blaizard/alarm/model/0001.png

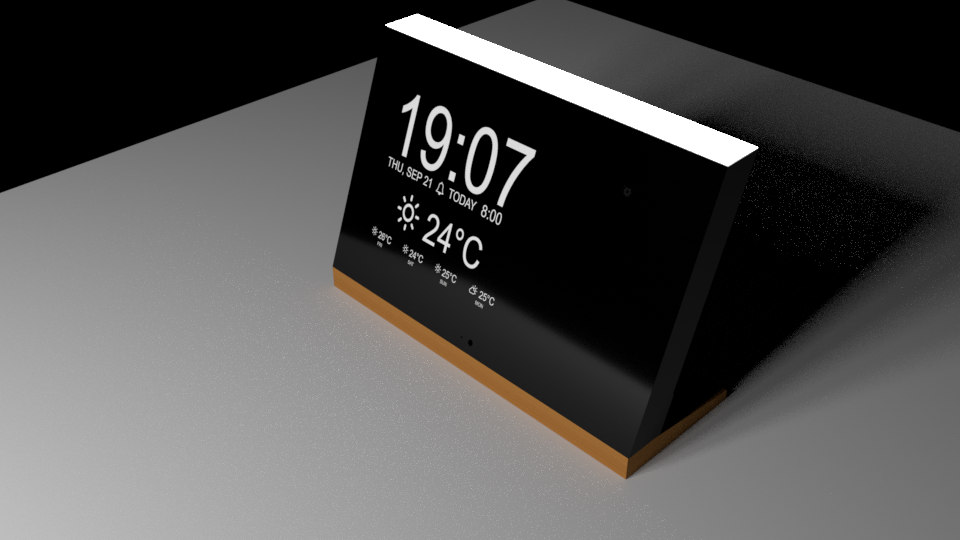
model/0001.png
