blaizard/alarm/model/default screen.jpg

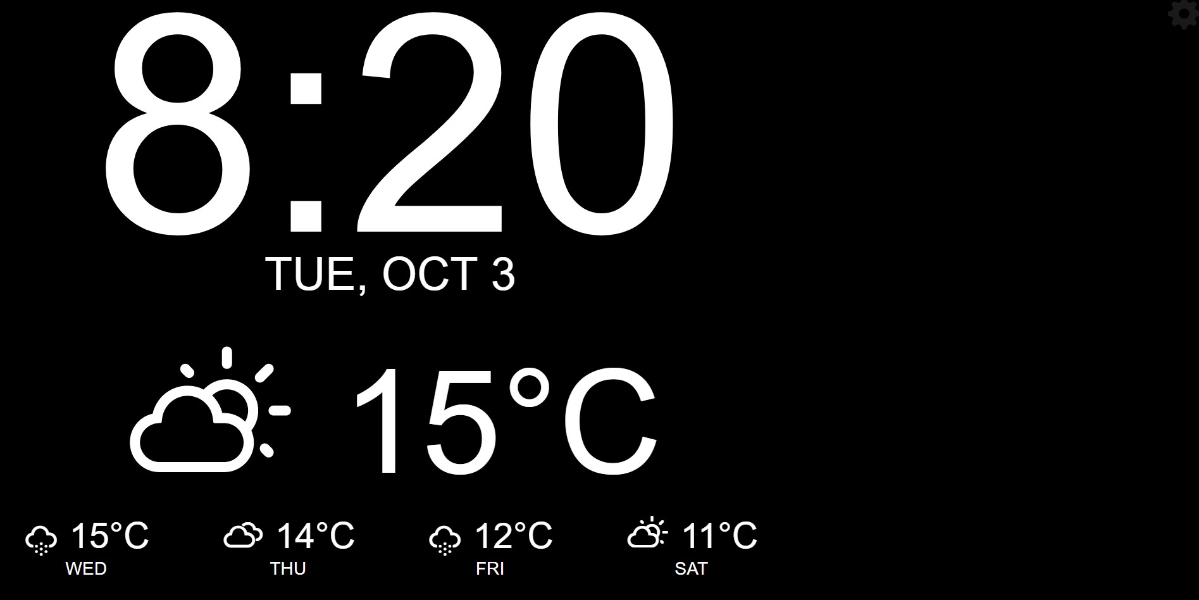
model/default screen.jpg
