blaizard/alarm/model/speaker.jpg

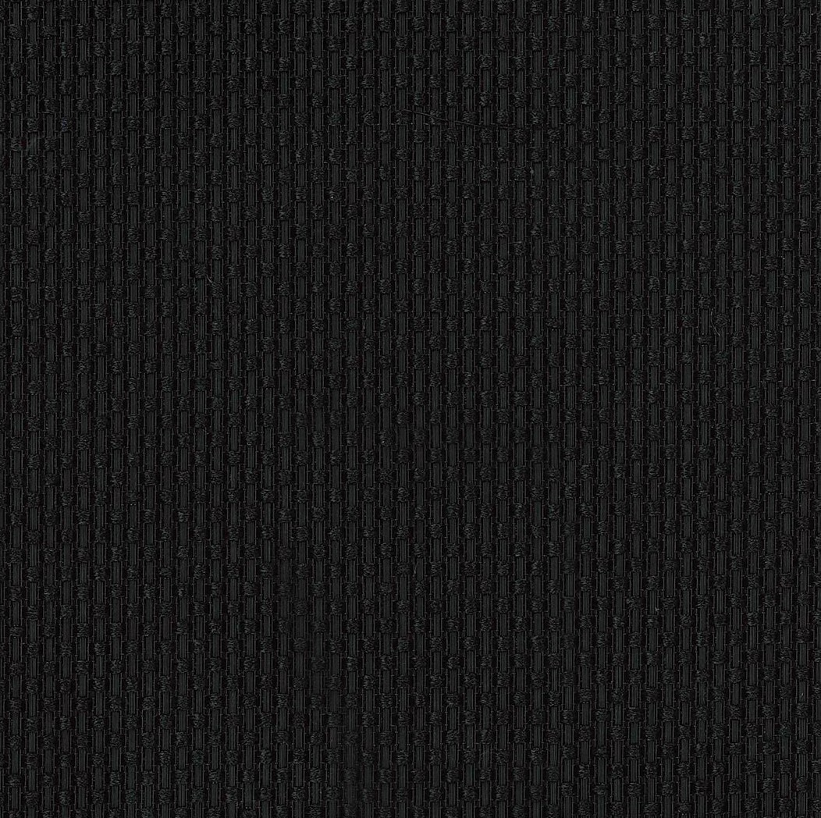
model/speaker.jpg
