blaizard/alarm/fw/samd21/GccQTouchApplication4/GccQTouchApplication4/touch.c

/* This source file is part of the ATMEL QTouch Library 5.0.7 */

/*****************************************************************************
 *
 * \file
 *
 * \brief  This file contains the SAMD QTouch library initialization,
 * sensor configuration and measurement routines.
 *
 *
 * - Userguide:          QTouch Library Peripheral Touch Controller User Guide.
 * - Support email:      www.atmel.com/design-support/
 *
 *
 * Copyright (c) 2013-2015 Atmel Corporation. All rights reserved.
 *
 * \asf_license_start
 *
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
 * 3. The name of Atmel may not be used to endorse or promote products derived
 *    from this software without specific prior written permission.
 *
 * 4. This software may only be redistributed and used in connection with an
 *    Atmel microcontroller product.
 *
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
 * \asf_license_stop
 *
 ******************************************************************************/

/*----------------------------------------------------------------------------
 *                               include files
 *
 *
 *----------------------------------------------------------------------------*/

/**
 * Includes for Touch Library.
 */

#include "touch_api_ptc.h"
#if (!defined(__D1x_NONASF__))
#include <asf.h>
#else
#define  NULL 0
#endif
/*----------------------------------------------------------------------------
 *                           manifest constants
 *
 *
 *----------------------------------------------------------------------------*/
#define   DEF_SELFCAP_CAL_SEQ1_COUNT                8
#define   DEF_SELFCAP_CAL_SEQ2_COUNT                4
#define DEF_SELFCAP_CC_CAL_CLK_PRESCALE_PER_NODE PRSC_DIV_SEL_1,PRSC_DIV_SEL_1,PRSC_DIV_SEL_1,PRSC_DIV_SEL_1
#define DEF_SELFCAP_CC_CAL_SENSE_RESISTOR_PER_NODE RSEL_VAL_0,RSEL_VAL_0,RSEL_VAL_0,RSEL_VAL_0
#define   DEF_SELFCAP_QUICK_REBURST_ENABLE          1u

/*----------------------------------------------------------------------------
 *                                   macros
 *
 *
 *----------------------------------------------------------------------------*/

/*----------------------------------------------------------------------------
 *                           type definitions
 *
 *
 *----------------------------------------------------------------------------*/

/*----------------------------------------------------------------------------
 *                           Structure Declarations
 *
 *
 *----------------------------------------------------------------------------*/

/*----------------------------------------------------------------------------
 *                               global variables
 *
 *
 *----------------------------------------------------------------------------*/
/* ! QTouch Library Timing info. */
touch_time_t touch_time;

/* ! QTouch Library acquisition status */
touch_acq_status_t  touch_acq_status;
/**
 * Mutual Cap sensors measured data pointer.
 * Note: This pointer is initialized by the QTouch library once the
 * touch_mutlcap_sensors_init API is called. */
touch_measure_data_t *p_mutlcap_measure_data = NULL;

/**
 * Self Cap sensors measured data pointer.
 * Note: This pointer is initialized by the QTouch library once the
 * touch_selfcap_sensors_init API is called. */
touch_measure_data_t *p_selfcap_measure_data = NULL;

/*----------------------------------------------------------------------------
 *                               static variables
 *
 *
 *----------------------------------------------------------------------------*/

/**
 * Self Cap sensors data block provided as input to Touch library.
 */
static uint8_t selfcap_data_blk[PRIV_SELFCAP_DATA_BLK_SIZE];

/**
 * Self Cap sensors Pins Info.
 */

uint32_t selfcap_y_nodes[DEF_SELFCAP_NUM_CHANNELS] = {DEF_SELFCAP_LINES};

filter_level_t selfcap_filter_level_per_node[DEF_SELFCAP_NUM_CHANNELS] = {DEF_SELFCAP_FILTER_LEVEL_PER_NODE};
	
uint8_t selfcap_auto_os_per_node[DEF_SELFCAP_NUM_CHANNELS]= {DEF_SELFCAP_AUTO_OS_PER_NODE};

gain_t selfcap_gain_per_node[DEF_SELFCAP_NUM_CHANNELS] = {DEF_SELFCAP_GAIN_PER_NODE};

rsel_val_t selfcap_resistor_per_node[DEF_SELFCAP_NUM_CHANNELS] = {DEF_SELFCAP_SENSE_RESISTOR_PER_NODE};

prsc_div_sel_t selfcap_prsc_per_node[DEF_SELFCAP_NUM_CHANNELS] = {DEF_SELFCAP_CLK_PRESCALE_PER_NODE};

prsc_div_sel_t selfcap_boot_prsc_per_node[DEF_SELFCAP_NUM_CHANNELS] = {DEF_SELFCAP_CC_CAL_CLK_PRESCALE_PER_NODE};

rsel_val_t selfcap_boot_resistor_per_node[DEF_SELFCAP_NUM_CHANNELS] = { DEF_SELFCAP_CC_CAL_SENSE_RESISTOR_PER_NODE};
	
freq_hop_sel_t selfcap_freq_hops[3u] = {DEF_SELFCAP_HOP_FREQS};

/**
 * Self Cap Configuration structure provided as input to Touch Library.
 *
 * Note: Use the touch.h configuration header file to fill in
 * the elements of this structure.  DO NOT modify any of the input values
 * directly in this structure.
 */
static touch_selfcap_config_t selfcap_config = {
	DEF_SELFCAP_NUM_CHANNELS,           /* Self Cap number of channels. */
	DEF_SELFCAP_NUM_SENSORS,            /* Self Cap number of sensors. */
	DEF_SELFCAP_NUM_ROTORS_SLIDERS,     /* Self Cap number of rotors and
	                                     * sliders. */

	/* Self Cap GLOBAL SENSOR CONFIGURATION INFO. */
	{
		DEF_SELFCAP_DI,                 /* uint8_t  di; Sensor detect
		                                 * integration (DI) limit. */

		/* Interchanging Negative and Positive Drift rate, since Signal
		 * increases on Touch. */
		DEF_SELFCAP_ATCH_DRIFT_RATE,    /* uint8_t  neg_drift_rate;
		                                 * Sensor
		                                 * negative drift rate. */
		DEF_SELFCAP_TCH_DRIFT_RATE,     /* uint8_t  pos_drift_rate;
		                                 * Sensor
		                                 * positive drift rate. */
		DEF_SELFCAP_MAX_ON_DURATION,    /* uint8_t  max_on_duration;
		                                 * Sensor
		                                 * maximum on duration. */
		DEF_SELFCAP_DRIFT_HOLD_TIME,    /* uint8_t  drift_hold_time;
		                                 * Sensor
		                                 * drift hold time. */
		DEF_SELFCAP_ATCH_RECAL_DELAY,   /* uint8_t  pos_recal_delay;
		                                 * Sensor positive recalibration
		                                 * delay. */

		DEF_SELFCAP_CAL_SEQ1_COUNT,
		DEF_SELFCAP_CAL_SEQ2_COUNT,
		DEF_SELFCAP_ATCH_RECAL_THRESHOLD, /* recal_threshold_t
		                                   * recal_threshold; Sensor
		                                   * recalibration threshold. */
		DEF_SELFCAP_TOUCH_POSTPROCESS_MODE,
        DEF_SELFCAP_AUTO_OS_SIGNAL_STABILITY_LIMIT,
		DEF_SELFCAP_FREQ_AUTO_TUNE_SIGNAL_STABILITY_LIMIT,
		DEF_SELFCAP_FREQ_AUTO_TUNE_IN_CNT,
		DEF_SELFCAP_NOISE_MEAS_SIGNAL_STABILITY_LIMIT, /* signal
		                                                *stability */
		DEF_SELFCAP_NOISE_LIMIT,
		DEF_SELFCAP_LOCKOUT_SEL,
		DEF_SELFCAP_LOCKOUT_CNTDOWN,
		#if ((SAMC20) || (SAMC21) || (SAML22))
		DEF_SELF_CAP_CSD_VALUE,
		#endif
	},
	{
		selfcap_gain_per_node,      /* Self Cap channel gain setting. */
		DEF_SELFCAP_FREQ_MODE,      /* Self Cap noise counter measure
		                             * enable/disable. */
		selfcap_prsc_per_node,
		selfcap_resistor_per_node,
		selfcap_boot_prsc_per_node,
		selfcap_boot_resistor_per_node,
		selfcap_freq_hops,
		selfcap_filter_level_per_node,   /* Self Cap filter level setting. */
		selfcap_auto_os_per_node,        /* Self Cap auto oversamples
		                             *setting. */
	},
	selfcap_data_blk,                   /* Self Cap data block index. */
	PRIV_SELFCAP_DATA_BLK_SIZE,         /* Self Cap data block size. */
	selfcap_y_nodes,                    /* Self Cap channel nodes. */
	DEF_SELFCAP_QUICK_REBURST_ENABLE,
	DEF_SELFCAP_FILTER_CALLBACK,         /* Self Cap filter callback
	                                      * function
	                                      * pointer. */
	DEF_SELFCAP_FREQ_AUTO_TUNE_ENABLE,
	DEF_SELFCAP_NOISE_MEAS_ENABLE,
	DEF_SELFCAP_NOISE_MEAS_BUFFER_CNT,
	DEF_SELFCAP_MOIS_TOLERANCE_ENABLE,
  	DEF_SELFCAP_NUM_MOIS_GROUPS,
    DEF_SELFCAP_MOIS_QUICK_REBURST_ENABLE,
    DEF_SELFCAP_PTC_GPIO_STATE,
	  .tlib_feature_list ={
		  .lk_chk = DEF_LOCKOUT_FUNC,
		  .auto_os_init = DEF_AUTO_OS_FUNC,//auto_os_resolve,
		  .auto_tune_init = DEF_SELF_AUTO_TUNE_FUNC,// self_auto_tuning
		  .enable_aks = DEF_AKS_FUNC, /*AKS grouping function */
	  }
};

/**
 * Touch Library input configuration structure.
 */
touch_config_t touch_config = {
	NULL,
	&selfcap_config,                /* Pointer to Self Cap configuration
	                                 * structure. */
	DEF_TOUCH_PTC_ISR_LVL,          /* PTC interrupt level. */
};

/*----------------------------------------------------------------------------
 *                               prototypes
 *
 *
 *----------------------------------------------------------------------------*/

/*! \brief configure keys, rotors and sliders.
 */
static touch_ret_t touch_sensors_config(void);

/*! \brief Self Cap measure complete callback function example prototype.
 */
void touch_selfcap_measure_complete_callback( void );

/*! \brief Initialize and enable PTC clock.
 */
void touch_configure_ptc_clock(void);

void touch_std_err_handle(void);

void __attribute__((optimize("O0"))) touch_app_err_handler(touch_app_err_t touch_app_err_val, touch_ret_t touch_lib_err_val);

/*----------------------------------------------------------------------------
 *  static functions
 *
 *
 *----------------------------------------------------------------------------*/

void touch_configure_ptc_clock(void)
{
#if (!defined(__D1x_NONASF__))
	struct system_gclk_chan_config gclk_chan_conf;

	system_gclk_chan_get_config_defaults(&gclk_chan_conf);

	gclk_chan_conf.source_generator = GCLK_GENERATOR_1;

	system_gclk_chan_set_config(PTC_GCLK_ID, &gclk_chan_conf);

	system_gclk_chan_enable(PTC_GCLK_ID);

	#if (SAML21)
    system_apb_clock_set_mask(SYSTEM_CLOCK_APB_APBD, MCLK_APBDMASK_PTC);
    #elif ((SAMC20) || (SAMC21) || (SAML22))
	system_apb_clock_set_mask(SYSTEM_CLOCK_APB_APBC, MCLK_APBCMASK_PTC);
	#else
    system_apb_clock_set_mask(SYSTEM_CLOCK_APB_APBC, PM_APBCMASK_PTC);
    #endif
#else
	PM->APBCMASK.reg |= (1u << 11u);
#endif
}

void touch_std_err_handle(void)
{
	for(;;)
	{
		
	}
}

void  __attribute__((optimize("O0"))) touch_app_err_handler(touch_app_err_t touch_app_err_val, touch_ret_t touch_lib_err_val)
{
	if(DEF_TOUCH_APP_ERR_HANDLER)
	
	{
	switch(touch_app_err_val)
	{
		case TOUCH_INIT_CONFIG_ERR:
				/*Probable reason: the touch_xxxxcap_sensors_init is fed with an
				 incompatible / incomplete parameter*/
				touch_std_err_handle();
				break;
		case TOUCH_SENSOR_CONFIG_ERR:
				/*Probable reason: touch_xxxxcap_sensor_config is fed with an incompatible
				 parameter / Library state is not INIT*/
				touch_std_err_handle();
				break;
		case TOUCH_INIT_CALIB_ERR:
				/*Probable reason: the touch_xxxxcap_sensors_calibrate is fed with an
				invalid parameter / the LIB state is NONE/BUSY */
				touch_std_err_handle();
				break;
		case TOUCH_MEASURE_INCOMPLETE:
				/* Reaching this point can be due to - The touch_measure api has error 
				due to a invalid input param / it was on an invalid Touch Library state*/
				touch_std_err_handle();
				break;				
		case TOUCH_MEASURE_CC_CAL_FAILED:
				/*Probable reason: Hardware calibration error, check the hardware,
                  and ensure it is proper, if the error persists check the user manual
				  for sensor design guidelines*/
				touch_std_err_handle();
				break;	
		default:
				touch_std_err_handle();	
				break;
	}
	}
}

/* ! [setup] */

/*! \brief Example application entry function.
 */
touch_ret_t touch_sensors_init(void)
{
	touch_ret_t touch_ret = TOUCH_SUCCESS;

	/* Setup and enable generic clock source for PTC module. */
	touch_configure_ptc_clock();

	touch_time.measurement_period_ms = DEF_TOUCH_MEASUREMENT_PERIOD_MS;

	/* Initialize touch library for Self Cap operation. */
	touch_ret = touch_selfcap_sensors_init(&touch_config);
	if (touch_ret != TOUCH_SUCCESS) {
		touch_app_err_handler(TOUCH_INIT_CONFIG_ERR, touch_ret);
	}

#if DEF_TOUCH_QDEBUG_ENABLE == 1
	QDebug_Init();
#endif

	/* configure the touch library sensors. */
	touch_ret = touch_sensors_config();
	if (touch_ret != TOUCH_SUCCESS) {
		touch_app_err_handler(TOUCH_SENSOR_CONFIG_ERR, touch_ret);
	}

	/* Auto Tuning setting for calibration.
	 *
	 * AUTO_TUNE_PRSC: When Auto tuning of pre-scaler is selected
	 * the PTC uses the user defined internal series resistor setting
	 * (DEF_MUTLCAP_SENSE_RESISTOR) and the pre-scaler is adjusted
	 * to slow down the PTC operation to ensure full charge transfer.
	 *
	 * AUTO_TUNE_RSEL: When Auto tuning of the series resistor is
	 * selected the PTC runs at user defined pre-scaler setting speed
	 * (DEF_MUTLCAP_CLK_PRESCALE) and the internal series resistor is
	 * tuned automatically to the optimum value to allow for full
	 * charge transfer.
	 *
	 * AUTO_TUNE_NONE: When manual tuning option is selected
	 *(AUTO_TUNE_NONE),
	 * the user defined values of PTC pre-scaler and series resistor is used
	 * for PTC operation as given in DEF_MUTLCAP_CLK_PRESCALE and
	 * DEF_MUTLCAP_SENSE_RESISTOR
	 *
	 */
	touch_ret = touch_selfcap_sensors_calibrate(DEF_SELF_AUTO_TUNE_VALUE);
	if (touch_ret != TOUCH_SUCCESS) {
		touch_app_err_handler(TOUCH_INIT_CALIB_ERR, touch_ret);
	}

	return (touch_ret);
}

touch_ret_t touch_sensors_measure(void)
{
	touch_ret_t touch_ret = TOUCH_SUCCESS;
    if (!(p_selfcap_measure_data->acq_status & TOUCH_CC_CALIB_ERROR) || (!DEF_TOUCH_APP_ERR_HANDLER))
       {

	if (touch_time.time_to_measure_touch == 1u) {
		touch_ret = touch_selfcap_sensors_measure(
				touch_time.current_time_ms,
				NORMAL_ACQ_MODE,
				touch_selfcap_measure_complete_callback);

		if ((touch_ret != TOUCH_ACQ_INCOMPLETE) &&
				(touch_ret == TOUCH_SUCCESS)) {
			touch_time.time_to_measure_touch = 0u;
		} else if ((touch_ret != TOUCH_SUCCESS) &&
				(touch_ret != TOUCH_ACQ_INCOMPLETE)) {
					touch_app_err_handler(TOUCH_MEASURE_INCOMPLETE, touch_ret);
			/* Reaching this point can be due to -
			 *     1. The api has retured an error due to a invalid
			 * input parameter.
			 *     2. The api has been called during a invalid Touch
			 * Library state. */
			 }
		}
	}
    else
    {
		/*
        To find which sensor failed in the calibration, check
         p_xxxxcap_measure_data->p_sensors[<sensor>].state == SENSOR_CALIBRATION_ERROR
        */
		touch_app_err_handler(TOUCH_MEASURE_CC_CAL_FAILED, touch_ret);
    }

	return (touch_ret);
}

/*! \brief Example configuration for touch keys, rotors and sliders.
 *
 * \retval TOUCH_SUCCESS   Configuration setting successful.
 * \retval TOUCH_INVALID_xx   Invalid input configuration setting.
 */
touch_ret_t touch_sensors_config(void)
{
	touch_ret_t touch_ret = TOUCH_SUCCESS;
	sensor_id_t sensor_id;

		touch_ret = touch_selfcap_sensor_config(SENSOR_TYPE_KEY, CHANNEL_0,CHANNEL_0, NO_AKS_GROUP, 10u, HYST_25,RES_8_BIT, &sensor_id);
	if (touch_ret != TOUCH_SUCCESS)
	{
		 touch_app_err_handler(TOUCH_SENSOR_CONFIG_ERR, touch_ret); 
	}


	touch_ret = touch_selfcap_sensor_config(SENSOR_TYPE_KEY, CHANNEL_1,CHANNEL_1, NO_AKS_GROUP, 10u, HYST_25,RES_8_BIT, &sensor_id);
	if (touch_ret != TOUCH_SUCCESS)
	{
		 touch_app_err_handler(TOUCH_SENSOR_CONFIG_ERR, touch_ret); 
	}


	touch_ret = touch_selfcap_sensor_config(SENSOR_TYPE_KEY, CHANNEL_2,CHANNEL_2, NO_AKS_GROUP, 10u, HYST_25,RES_8_BIT, &sensor_id);
	if (touch_ret != TOUCH_SUCCESS)
	{
		 touch_app_err_handler(TOUCH_SENSOR_CONFIG_ERR, touch_ret); 
	}


	touch_ret = touch_selfcap_sensor_config(SENSOR_TYPE_KEY, CHANNEL_3,CHANNEL_3, NO_AKS_GROUP, 10u, HYST_25,RES_8_BIT, &sensor_id);
	if (touch_ret != TOUCH_SUCCESS)
	{
		 touch_app_err_handler(TOUCH_SENSOR_CONFIG_ERR, touch_ret); 
	}






	return (touch_ret);
}

/*! \brief Self Cap measure complete callback function.
 *
 * This function is called by the library when the touch measurement
 * process for Self Cap sensors is completed.
 *
 * \param p_measure_data   Base address of touch_measure_data_t instance.
 * \note A touch_selfcap_measure_complete_callback() call signifies that fresh
 * values of touch status, rotor/slider position, measured signals,
 * references and Sensor data is available.
 * The Self Cap measured data can be accessed using the p_measure_data
 * pointer.
 */
void touch_selfcap_measure_complete_callback( void )
{
#if DEF_TOUCH_QDEBUG_ENABLE == 1

	/* Send out the Touch debug information data each time when Touch
	 *   measurement process is completed .
	 *   The Touch Signal and Touch Delta values are always sent.
	 *   Touch Status change, Rotor-Slider Position change and Sensor
	 * Reference
	 *   values can be optionally sent using the masks below.
	 */
	QDebug_SendData( TOUCH_CHANNEL_REF_CHANGE |
			TOUCH_ROTOR_SLIDER_POS_CHANGE |
			TOUCH_STATUS_CHANGE );

	/* QT600 two-way QDebug communication application Example. */
	/* Process any commands received from QTouch Studio. */
	QDebug_ProcessCommands();
#endif

	if (!(p_selfcap_measure_data->acq_status & TOUCH_BURST_AGAIN)) {
		/* Set the QTouch measurement done flag. */
		p_selfcap_measure_data->measurement_done_touch = 1u;
		touch_acq_status = p_selfcap_measure_data->acq_status;
	}
}
